MelansonTech/Melanson-Tech-Isolated-Shunt-Amplifier/Revision 1/TestData/BodePlots/1khz-10Meghz Gain 10x  0r010Shunt.xlsx

Untitled | Untitled 1 | Untitled 2 | Untitled 3
1000 | -0.166787 | -0.385627 | 0.336464
1258.925412 | -0.242249 | -0.413234 | 0.500956
1584.893192 | -0.150085 | -0.622799 | 0.415946
1995.262315 | -0.188624 | -0.812734 | 0.337932
2511.886432 | -0.183692 | -0.066411 | 0.445627
3162.27766 | -0.216886 | -0.911619 | 0.363395
3981.071706 | -0.248103 | -1.11181 | 0.502347
5011.872336 | -0.313746 | -1.38651 | 0.618555
6309.573445 | -0.263741 | -1.232366 | 0.56154
7943.282347 | -0.242898 | -1.544541 | 0.517559
10000 | -0.223894 | -1.853628 | 0.456404
12589.25412 | -0.209771 | -1.966123 | 0.607302
15848.93193 | -0.226493 | -3.019898 | 0.567094
19952.62315 | -0.173401 | -3.595255 | 0.597347
25118.86431 | -0.079341 | -4.264827 | 0.578082
31622.7766 | -0.080549 | -6.481584 | 0.593097
39810.71706 | 0.010377 | -8.275535 | 0.615941
50118.72336 | 0.131881 | -10.449231 | 0.556628
63095.73445 | 0.219651 | -13.857448 | 0.810801
79432.82347 | 0.352913 | -18.403695 | 0.686286
100000 | 0.480244 | -23.968928 | 0.706028
125892.5412 | 0.599213 | -30.235161 | 1.015421
158489.3192 | 0.776089 | -40.437328 | 0.848043
199526.2315 | 0.894499 | -51.551826 | 0.954622
251188.6432 | 1.355552 | -67.514444 | 1.121187
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
