MelansonTech/Melanson-Tech-Isolated-Shunt-Amplifier/Revision 1/TestData/BodePlots/1khz-10Meghz Gain 10x  0r010Shunt_1.xlsx

Untitled | Untitled 1 | Untitled 2 | Untitled 3
1000 | -0.164963 | -0.309048 | 0.379071
1079.775162 | -0.128116 | -0.219387 | 0.326995
1165.914401 | -0.161152 | -1.027728 | 0.403795
1258.925412 | -0.179917 | 0.23005 | 0.382496
1359.356391 | -0.142654 | -0.262303 | 0.411716
1467.799268 | -0.14915 | -0.528165 | 0.508479
1584.893192 | -0.144146 | -0.680492 | 0.357872
1711.328304 | -0.17431 | -0.493263 | 0.492636
1847.849797 | -0.179099 | -0.608428 | 0.557685
1995.262315 | -0.182238 | -0.674658 | 0.437536
2154.43469 | -0.187685 | -0.645897 | 0.421993
2326.305067 | -0.190564 | -0.792882 | 0.41525
2511.886432 | -0.228326 | -0.459325 | 0.386465
2712.272579 | -0.238131 | -0.811535 | 0.41732
2928.644565 | -0.208502 | -0.919118 | 0.406281
3162.27766 | -0.202652 | -0.95411 | 0.446176
3414.548874 | -0.216239 | -1.168893 | 0.458934
3686.945065 | -0.225559 | -0.89491 | 0.438337
3981.071706 | -0.226103 | -1.056473 | 0.480328
4298.662347 | -0.228212 | -1.099326 | 0.539283
4641.588834 | -0.244441 | -1.147914 | 0.468855
5011.872336 | -0.354077 | -0.637942 | 0.491152
5411.695265 | -0.244513 | -1.14488 | 0.51443
5843.414134 | -0.252042 | -1.434539 | 0.56404
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
