MelansonTech/Melanson-Tech-Isolated-Shunt-Amplifier/Revision 1/TestData/BodePlots/SI8921B-modifed/100khz-1000khz Gain 10x  0r010Shunt_3.3nf output filt C23-560pF - x50 filt cap 560pF.xlsx

Untitled | Untitled 1 | Untitled 2 | Untitled 3
1000 | -0.007271 | -0.572757 | 0.418006
1258.925412 | 0.077268 | -0.539768 | 0.400527
1584.893192 | -0.0003 | -0.723423 | 0.354738
1995.262315 | -0.01521 | -0.96655 | 0.359529
2511.886432 | -0.036307 | -1.231762 | 0.465736
3162.27766 | -0.059285 | -1.440721 | 0.452594
3981.071706 | -0.050049 | -1.825088 | 0.463353
5011.872336 | 0.00812 | -2.12929 | 0.626424
6309.573445 | -0.058686 | -2.53885 | 0.44223
7943.282347 | -0.059571 | -3.166069 | 0.462066
10000 | -0.060859 | -4.022216 | 0.529905
12589.25412 | -0.078112 | -5.213084 | 0.409742
15848.93193 | -0.039617 | -6.37527 | 0.570275
19952.62315 | 0.025826 | -8.159199 | 0.578589
25118.86431 | 0.125273 | -10.326592 | 0.628492
31622.7766 | 0.079798 | -13.222132 | 0.669211
39810.71706 | 0.114622 | -16.875604 | 0.748752
50118.72336 | 0.233843 | -21.505801 | 1.002004
63095.73445 | 0.16181 | -27.848137 | 0.795671
79432.82347 | 0.245553 | -35.295127 | 0.728898
100000 | 0.281433 | -45.062021 | 0.704041
125892.5412 | 0.12971 | -55.566231 | 0.908138
158489.3192 | 0.199942 | -73.108045 | 0.584394
199526.2315 | 0.116589 | -92.47451 | 0.797795
251188.6432 | -0.413037 | -119.043982 | 1.130682
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
