MelansonTech/Melanson-Tech-Isolated-Shunt-Amplifier/Revision 1/TestData/BodePlots/SI8921B-modifed/100khz-1000khz Gain 10x  0r010Shunt_3.3nf output filt C23-560pF.xlsx

Untitled | Untitled 1 | Untitled 2 | Untitled 3
100000 | 0.313502 | -41.958272 | 0.688879
125892.5412 | 0.387259 | -53.4945 | 0.875311
158489.3192 | 0.308083 | -67.947277 | 0.981933
199526.2315 | 0.115216 | -86.545426 | 0.829072
251188.6432 | -0.330637 | -107.270166 | 1.272936
316227.766 | -0.340213 | -139.088437 | 1.313568
398107.1706 | -0.810289 | -178.106699 | 1.503704
501187.2336 | -2.888756 | 126.559879 | 1.510791
630957.3445 | -5.692802 | 67.801909 | 1.687902
794328.2347 | -11.639043 | 0.706496 | 2.282123
1000000 | -17.937818 | -89.865859 | 8.847568
