MelansonTech/Melanson-Tech-Isolated-Shunt-Amplifier/Revision 1/TestData/BodePlots/SI8921B-modifed/100khz-1000khz Gain 50x  0r010Shunt_3.3nf output filt C23-560pF.xlsx

Untitled | Untitled 1 | Untitled 2 | Untitled 3
1000 | 0.064522 | -0.713499 | 0.825991
1258.925412 | 0.195579 | -1.837927 | 0.762102
1584.893192 | 0.099175 | -1.392925 | 0.747944
1995.262315 | 0.066472 | -1.645283 | 0.754356
2511.886432 | 0.068113 | -2.95294 | 0.716811
3162.27766 | 0.024284 | -2.597538 | 0.894711
3981.071706 | 0.010385 | -2.998652 | 0.720921
5011.872336 | 0.078165 | -4.980822 | 0.804446
6309.573445 | -0.016736 | -4.539137 | 0.83104
7943.282347 | -0.005151 | -5.303585 | 0.721352
10000 | -0.023023 | -6.788479 | 0.839424
12589.25412 | 0.063563 | -9.723817 | 0.912994
15848.93193 | -0.011544 | -10.399116 | 0.815987
19952.62315 | -0.036871 | -13.273732 | 0.986796
25118.86431 | 0.063136 | -17.025937 | 0.61663
31622.7766 | -0.061974 | -21.224436 | 0.837353
39810.71706 | -0.025154 | -26.655559 | 1.012666
50118.72336 | 0.028295 | -32.734162 | 0.830485
63095.73445 | -0.151455 | -42.932902 | 1.357885
79432.82347 | -0.375164 | -54.226394 | 1.439817
100000 | -0.672215 | -67.874812 | 1.704844
125892.5412 | -1.923903 | -82.940608 | 1.889883
158489.3192 | -1.967661 | -106.971336 | 2.29011
199526.2315 | -3.207152 | -131.090175 | 2.251656
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
