MelansonTech/Melanson-Tech-Isolated-Shunt-Amplifier/Revision 1/TestData/BodePlots/SI8921B-modifed/100khz-100khz Gain 50x  0r010Shunt_3.3nf output filt C23-560pF - x50 filt cap 560pF.xlsx

Untitled | Untitled 1 | Untitled 2 | Untitled 3
1000 | 0.05207 | -1.963352 | 0.942213
1258.925412 | 0.197826 | -4.049852 | 0.917636
1584.893192 | 0.071184 | -3.003377 | 0.739586
1995.262315 | 0.039404 | -3.660843 | 0.793368
2511.886432 | 0.101302 | -5.543226 | 0.779344
3162.27766 | -0.014446 | -5.522928 | 0.740511
3981.071706 | -0.029404 | -7.030474 | 0.796969
5011.872336 | 0.05596 | -9.691169 | 0.747881
6309.573445 | -0.105583 | -10.825865 | 0.732612
7943.282347 | -0.118312 | -13.497003 | 0.750385
10000 | -0.181516 | -17.000783 | 0.781518
12589.25412 | -0.160564 | -20.839707 | 0.88175
15848.93193 | -0.395699 | -26.29038 | 0.732019
19952.62315 | -0.556081 | -32.826666 | 0.730841
25118.86431 | -0.858598 | -42.349229 | 1.010743
31622.7766 | -1.349577 | -50.452464 | 0.886223
39810.71706 | -1.926483 | -61.54613 | 0.655165
50118.72336 | -2.974799 | -76.441642 | 0.9142
63095.73445 | -3.834709 | -90.704306 | 0.788833
79432.82347 | -5.340546 | -108.032392 | 0.944281
100000 | -7.123333 | -126.834246 | 0.977973
