MelansonTech/Melanson-Tech-Isolated-Shunt-Amplifier/Revision 1/TestData/BodePlots/SI8921B-modifed/1khz-1000khz Gain 10x  0r010Shunt_3.3nf output filt C23-560pF - x50 filt cap 560pF filt cap2 47nF.xlsx

Untitled | Untitled 1 | Untitled 2 | Untitled 3
1000 | -0.001412 | -0.491789 | 0.386197
1258.925412 | 0.051911 | -0.882857 | 0.382758
1584.893192 | -0.002914 | -0.627658 | 0.3803
1995.262315 | -0.004918 | -0.985267 | 0.391553
2511.886432 | 0.058918 | -0.762546 | 0.44308
3162.27766 | -0.03218 | -1.502325 | 0.417804
3981.071706 | -0.047722 | -1.692322 | 0.447256
5011.872336 | -0.068907 | -2.207698 | 0.52855
6309.573445 | -0.031446 | -2.486523 | 0.346339
7943.282347 | -0.03868 | -3.176357 | 0.403295
10000 | -0.035435 | -4.062742 | 0.529503
12589.25412 | 0.118613 | -5.158486 | 0.474753
15848.93193 | 0.008463 | -6.300188 | 0.509958
19952.62315 | 0.037662 | -8.071385 | 0.50475
25118.86431 | 0.045896 | -11.128869 | 0.686767
31622.7766 | 0.071791 | -13.162034 | 0.622529
39810.71706 | 0.154046 | -16.970277 | 0.615668
50118.72336 | 0.138483 | -21.865062 | 0.714991
63095.73445 | 0.204389 | -28.370627 | 0.828323
79432.82347 | 0.26264 | -35.456147 | 0.795539
100000 | 0.289751 | -45.445786 | 0.623059
125892.5412 | -0.226415 | -55.959106 | 0.780761
158489.3192 | 0.161721 | -73.118075 | 0.864599
199526.2315 | 0.007809 | -92.832452 | 1.103654
251188.6432 | -0.325714 | -118.690986 | 1.269356
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
