MelansonTech/Melanson-Tech-Isolated-Shunt-Amplifier/Revision 1/TestData/BodePlots/SI8921B-modifed/1khz-1000khz Gain 10x  0r010Shunt_3.3nf output filt C23-560pF.xlsx

Untitled | Untitled 1 | Untitled 2 | Untitled 3
1000 | -0.029164 | -0.415758 | 0.409154
1258.925412 | 0.051928 | -0.653245 | 0.450997
1584.893192 | 0.008203 | -0.673949 | 0.384839
1995.262315 | -0.003543 | -0.855599 | 0.388993
2511.886432 | -0.028419 | -1.35738 | 0.394654
3162.27766 | -0.029335 | -1.346178 | 0.401389
3981.071706 | -0.046099 | -1.487113 | 0.375325
5011.872336 | -0.088454 | -1.963935 | 0.467691
6309.573445 | -0.040359 | -2.587683 | 0.367528
7943.282347 | -0.039981 | -2.78341 | 0.512421
10000 | -0.030514 | -3.598115 | 0.436275
12589.25412 | 0.052237 | -4.786346 | 0.506834
15848.93193 | 0.015761 | -5.972702 | 0.533102
19952.62315 | 0.048069 | -7.253569 | 0.629485
25118.86431 | 0.112095 | -8.332555 | 0.620274
31622.7766 | 0.151572 | -12.033556 | 0.669804
39810.71706 | 0.187474 | -15.449311 | 0.57619
50118.72336 | 0.348314 | -20.808378 | 0.752883
63095.73445 | 0.304537 | -25.765356 | 0.763022
79432.82347 | 0.328061 | -32.978392 | 0.748215
100000 | 0.354872 | -42.197753 | 0.654933
125892.5412 | 0.250991 | -51.815006 | 0.888359
158489.3192 | 0.305403 | -67.868428 | 0.809862
199526.2315 | 0.134738 | -86.163011 | 0.788386
251188.6432 | -0.074423 | -110.093568 | 1.306668
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
