MelansonTech/Melanson-Tech-Isolated-Shunt-Amplifier/Revision 1/TestData/BodePlots/SI8921B-modifed/1khz-100khz Gain 50x  0r010Shunt_3.3nf output filt C23-560pF - x50 filt cap 560pF filt cap2 47nF.xlsx

Untitled | Untitled 1 | Untitled 2 | Untitled 3
1000 | 0.071029 | -3.649681 | 0.701021
1258.925412 | 0.25024 | -5.870788 | 0.806356
1584.893192 | 0.064123 | -5.633435 | 0.673676
1995.262315 | 0.04073 | -7.223179 | 0.845832
2511.886432 | 0.15908 | -9.99452 | 0.822513
3162.27766 | -0.052469 | -11.215229 | 0.658098
3981.071706 | -0.085104 | -14.04281 | 0.714957
5011.872336 | -0.041204 | -18.347498 | 0.854144
6309.573445 | -0.255909 | -21.661879 | 0.841967
7943.282347 | -0.369085 | -27.022767 | 0.90138
10000 | -0.556596 | -33.566681 | 0.999071
12589.25412 | -0.6651 | -41.955037 | 1.026333
15848.93193 | -1.34603 | -51.607566 | 0.877883
19952.62315 | -1.996641 | -63.266367 | 0.854583
25118.86431 | -3.127706 | -76.344589 | 0.893428
31622.7766 | -4.274065 | -92.964914 | 0.907988
39810.71706 | -5.980007 | -110.229574 | 1.189904
50118.72336 | -8.540003 | -129.364359 | 1.175728
63095.73445 | -10.794905 | -150.328231 | 1.426667
79432.82347 | -14.107479 | -171.989133 | 2.210238
100000 | -17.905938 | 165.209907 | 5.050973
