MelansonTech/Melanson-Tech-Isolated-Shunt-Amplifier/Revision 1/TestData/BodePlots/SI8921B-modifed/1khz-800khz Gain 10x  0r010Shunt_3.3nf output filt.xlsx

Untitled | Untitled 1 | Untitled 2 | Untitled 3
1000 | 0.007174 | -0.387205 | 0.400885
1258.925412 | 0.045516 | -0.304139 | 0.429812
1584.893192 | 0.013161 | -0.63136 | 0.355633
1995.262315 | 0.002602 | -0.874513 | 0.411591
2511.886432 | -0.018299 | -1.251431 | 0.381355
3162.27766 | -0.034086 | -1.198722 | 0.366614
3981.071706 | -0.052975 | -1.567748 | 0.383089
5011.872336 | -0.101388 | -2.345715 | 0.369202
6309.573445 | -0.049839 | -2.11402 | 0.478531
7943.282347 | -0.041625 | -2.653531 | 0.416471
10000 | -0.036766 | -3.265254 | 0.398806
12589.25412 | -0.035812 | -4.308069 | 0.607169
15848.93193 | 0.04319 | -5.508472 | 0.54892
19952.62315 | 0.056539 | -6.856632 | 0.482075
25118.86431 | 0.282153 | -8.498182 | 0.818443
31622.7766 | 0.142533 | -11.072022 | 0.608683
39810.71706 | 0.214596 | -14.57403 | 0.459452
50118.72336 | 0.231782 | -19.186235 | 1.108948
63095.73445 | 0.294758 | -23.97433 | 0.719064
79432.82347 | 0.419715 | -30.905854 | 0.901599
100000 | 0.54491 | -39.832185 | 0.638091
125892.5412 | 0.48953 | -49.518875 | 0.84785
158489.3192 | 0.550398 | -65.048945 | 0.820462
199526.2315 | 0.608525 | -83.836701 | 0.648542
251188.6432 | 0.476222 | -108.164402 | 0.913757
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
