MelansonTech/Melanson-Tech-Isolated-Shunt-Amplifier/Revision 1/TestData/BodePlots/SI8921B-modifed/1khz-800khz Gain 10x  0r010Shunt_3.3nf output filt_1.xlsx

Untitled | Untitled 1 | Untitled 2 | Untitled 3
1000 | -0.011512 | -0.400714 | 0.342174
1258.925412 | 0.025063 | -0.880549 | 0.415367
1584.893192 | 0.018192 | -0.721981 | 0.420674
1995.262315 | 0.003419 | -0.833224 | 0.403585
2511.886432 | 0.015298 | -1.158992 | 0.400182
3162.27766 | -0.052222 | -1.268797 | 0.398517
3981.071706 | -0.049142 | -1.533551 | 0.413095
5011.872336 | -0.01116 | -2.216545 | 0.377675
6309.573445 | -0.052252 | -2.190339 | 0.533511
7943.282347 | -0.035679 | -2.711656 | 0.596563
10000 | -0.038416 | -3.271058 | 0.461868
12589.25412 | 0.094113 | -4.486929 | 0.544178
15848.93193 | 0.041698 | -5.391758 | 0.565729
19952.62315 | 0.06628 | -6.991664 | 0.59351
25118.86431 | 0.2137 | -8.668189 | 0.624129
31622.7766 | 0.132644 | -11.482407 | 0.66954
39810.71706 | 0.20789 | -14.715592 | 0.832414
50118.72336 | 0.360193 | -19.034826 | 0.659566
63095.73445 | 0.367586 | -24.342496 | 0.746998
79432.82347 | 0.401086 | -31.224258 | 0.883342
100000 | 0.471592 | -40.172128 | 0.821223
125892.5412 | 0.364402 | -49.968074 | 1.061229
158489.3192 | 0.610198 | -66.053959 | 0.822275
199526.2315 | 0.640646 | -83.803273 | 0.649341
251188.6432 | 0.171551 | -108.385574 | 1.39107
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
