MelansonTech/Melanson-Tech-Isolated-Shunt-Amplifier/Revision 1/TestData/BodePlots/SI8921B-modifed/1khz-800khz Gain 50x  0r010Shunt_3.3nf output filt C23-680pF.xlsx

Untitled | Untitled 1 | Untitled 2 | Untitled 3
100000 | 0.125335 | -44.095085 | 0.659089
125892.5412 | -0.27493 | -55.399287 | 0.824094
158489.3192 | -0.171427 | -70.275468 | 1.0017
199526.2315 | -0.391973 | -88.667018 | 0.886321
251188.6432 | -0.718177 | -113.174029 | 0.872392
316227.766 | -0.987231 | -139.91413 | 1.307415
398107.1706 | -1.628402 | -178.534868 | 1.041197
501187.2336 | -3.15011 | 125.299528 | 1.797763
630957.3445 | -6.27653 | 67.748488 | 1.955576
794328.2347 | -12.194439 | 1.348629 | 2.595551
1000000 | -19.093066 | -77.022631 | 7.16214
