MelansonTech/Melanson-Tech-Isolated-Shunt-Amplifier/Revision 1/TestData/BodePlots/SI8921B-modifed/1khz-800khz Gain 50x  0r010Shunt_3.3nf output filt.xlsx

Untitled | Untitled 1 | Untitled 2 | Untitled 3
1000 | 0.054281 | -0.672905 | 0.793062
1258.925412 | 0.170075 | -1.723295 | 0.784336
1584.893192 | 0.081743 | -1.191481 | 0.767433
1995.262315 | 0.062793 | -1.538392 | 0.818119
2511.886432 | 0.147071 | -2.645347 | 0.845907
3162.27766 | -0.003843 | -2.208584 | 0.847037
3981.071706 | 0.008742 | -2.786028 | 0.736751
5011.872336 | 0.039246 | -4.215678 | 0.802545
6309.573445 | -0.027557 | -4.0071 | 0.901875
7943.282347 | -0.027034 | -4.934049 | 0.770238
10000 | -0.03041 | -6.192249 | 0.822031
12589.25412 | 0.046377 | -8.37912 | 0.744522
15848.93193 | 0.001363 | -10.06228 | 0.93926
19952.62315 | -0.024831 | -12.176484 | 1.018673
25118.86431 | 0.036893 | -16.185266 | 0.853329
31622.7766 | 0.024304 | -19.567205 | 0.875395
39810.71706 | 0.075147 | -24.680836 | 1.123904
50118.72336 | -0.131459 | -31.30462 | 1.181298
63095.73445 | -0.029736 | -40.1159 | 1.648383
79432.82347 | -0.102527 | -50.902239 | 1.566692
100000 | -0.279003 | -64.228459 | 1.872802
125892.5412 | -1.556058 | -79.621167 | 2.400331
158489.3192 | -1.220001 | -102.288345 | 2.809618
199526.2315 | -2.305808 | -127.616955 | 2.577078
251188.6432 | -3.266524 | -155.787252 | 2.731802
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
