MelansonTech/Melanson-Tech-Isolated-Shunt-Amplifier/Revision 1/TestData/BodePlots/SI8921B/100hz-1Mkhz Gain 100x  0r010Shunt_2.2nf output filt.xlsx

Untitled | Untitled 1 | Untitled 2 | Untitled 3
100 | 0.006271 | -0.068033 | 0.27774
125.892541 | -0.026333 | 0.222918 | 0.290215
158.489319 | 0.003324 | 0.042885 | 0.329393
199.526231 | -0.006859 | 0.049974 | 0.350675
251.188643 | -0.00971 | -0.275637 | 0.354524
316.227766 | 7.2e-05 | 0.090136 | 0.290524
398.107171 | -0.006296 | 0.0268 | 0.326617
501.187234 | 0.069499 | 0.150467 | 0.299249
630.957344 | 0.014773 | 0.012803 | 0.286016
794.328235 | 0.037272 | 0.165785 | 0.346965
1000 | 0.024027 | 0.075002 | 0.388099
1258.925412 | 0.105147 | -0.28254 | 0.356661
1584.893192 | 0.065292 | -0.021393 | 0.40356
1995.262315 | 0.05624 | -0.055238 | 0.401904
2511.886432 | 0.049367 | 0.192684 | 0.400087
3162.27766 | 0.071064 | -0.111055 | 0.427408
3981.071706 | 0.0964 | -0.065856 | 0.372432
5011.872336 | 0.149708 | -0.680933 | 0.414754
6309.573445 | 0.190248 | -0.612579 | 0.374768
7943.282347 | 0.256524 | -0.993632 | 0.388619
10000 | 0.326169 | -1.776701 | 0.412916
12589.25412 | 0.357161 | -2.962147 | 0.540464
15848.93193 | 0.420766 | -4.036209 | 0.661014
19952.62315 | 0.464666 | -5.588194 | 0.489353
25118.86431 | 0.612346 | -8.454723 | 0.608499
31622.7766 | 0.560109 | -10.081403 | 0.549657
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
