MelansonTech/Melanson-Tech-Isolated-Shunt-Amplifier/Revision 1/TestData/BodePlots/SI8921B/100hz-1Mkhz Gain 100x  0r010Shunt_3.3nf output filt.xlsx

Untitled | Untitled 1 | Untitled 2 | Untitled 3
100 | -0.022282 | -0.058049 | 0.313225
125.892541 | -0.044786 | -0.046411 | 0.296977
158.489319 | -0.024129 | 0.030752 | 0.380635
199.526231 | -0.005085 | 0.061221 | 0.346586
251.188643 | -0.053261 | -0.192632 | 0.401592
316.227766 | -0.005653 | 0.169307 | 0.325114
398.107171 | -0.016431 | 0.099411 | 0.332158
501.187234 | 0.010859 | -0.084321 | 0.328726
630.957344 | 0.009812 | -0.043785 | 0.368432
794.328235 | 0.030827 | 0.10783 | 0.391994
1000 | 0.021412 | 0.023076 | 0.334639
1258.925412 | 0.028485 | -0.340813 | 0.349454
1584.893192 | 0.061199 | 0.012489 | 0.371446
1995.262315 | 0.050718 | -0.149597 | 0.384132
2511.886432 | 0.052177 | -0.195681 | 0.47576
3162.27766 | 0.057638 | -0.224039 | 0.436108
3981.071706 | 0.088252 | -0.256186 | 0.328084
5011.872336 | 0.102445 | -0.62421 | 0.375166
6309.573445 | 0.20179 | -0.731505 | 0.366793
7943.282347 | 0.247345 | -1.369095 | 0.381789
10000 | 0.320085 | -2.050848 | 0.402476
12589.25412 | 0.322192 | -3.010692 | 0.365105
15848.93193 | 0.427328 | -4.69689 | 0.474706
19952.62315 | 0.466185 | -6.319212 | 0.464672
25118.86431 | 0.497584 | -7.890442 | 0.594781
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
