MelansonTech/Melanson-Tech-Isolated-Shunt-Amplifier/Revision 1/TestData/BodePlots/SI8921B/100hz-1Mkhz Gain 100x  0r010Shunt_4nf output filt.xlsx

Untitled | Untitled 1 | Untitled 2 | Untitled 3
100 | -0.011646 | -0.186644 | 0.324419
125.892541 | -0.008848 | -0.470833 | 0.374328
158.489319 | 0.000513 | -0.054358 | 0.332091
199.526231 | -0.014627 | 0.00252 | 0.31939
251.188643 | -0.035922 | -0.133026 | 0.338004
316.227766 | -0.003355 | 0.055016 | 0.286123
398.107171 | -0.020003 | 0.102376 | 0.351795
501.187234 | 0.130507 | -0.197465 | 0.432652
630.957344 | 0.016004 | 0.028714 | 0.370028
794.328235 | 0.027295 | 0.040367 | 0.362361
1000 | 0.021116 | 0.040315 | 0.331496
1258.925412 | 0.028183 | 0.166917 | 0.348732
1584.893192 | 0.035851 | -0.121835 | 0.417872
1995.262315 | 0.05675 | -0.181759 | 0.420646
2511.886432 | 0.10589 | -0.397403 | 0.394932
3162.27766 | 0.073821 | -0.241463 | 0.400716
3981.071706 | 0.104705 | -0.412814 | 0.427394
5011.872336 | 0.202215 | -0.87855 | 0.446382
6309.573445 | 0.215852 | -0.99377 | 0.364387
7943.282347 | 0.247451 | -1.597763 | 0.380991
10000 | 0.319096 | -2.297543 | 0.426298
12589.25412 | 0.426062 | -3.911501 | 0.507399
15848.93193 | 0.418839 | -5.079229 | 0.549556
19952.62315 | 0.465758 | -7.025158 | 0.553534
25118.86431 | 0.623222 | -8.69878 | 0.623135
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
