MelansonTech/Melanson-Tech-Isolated-Shunt-Amplifier/Revision 1/TestData/BodePlots/SI8921B/100hz-200khz Gain 100x  0r010Shunt_4.7nf output filt.xlsx

Untitled | Untitled 1 | Untitled 2 | Untitled 3
100 | -0.018273 | 0.063398 | 0.346112
125.892541 | 0.047429 | -0.108282 | 0.349609
158.489319 | -0.017419 | 0.007446 | 0.314467
199.526231 | -0.008665 | -0.04091 | 0.364519
251.188643 | -0.003899 | -0.112408 | 0.355988
316.227766 | -0.008815 | -0.03527 | 0.287034
398.107171 | -0.014407 | 0.063112 | 0.321475
501.187234 | 0.059367 | -0.076349 | 0.43115
630.957344 | 0.011782 | -0.062217 | 0.329315
794.328235 | 0.018064 | 0.046277 | 0.398337
1000 | 0.024427 | 0.038161 | 0.345292
1258.925412 | 0.164085 | -0.389204 | 0.359969
1584.893192 | 0.063465 | -0.091607 | 0.383588
1995.262315 | 0.059882 | -0.103315 | 0.363583
2511.886432 | 0.066218 | -0.417576 | 0.414248
3162.27766 | 0.074538 | -0.325521 | 0.420616
3981.071706 | 0.10865 | -0.417827 | 0.368795
5011.872336 | 0.217314 | -0.364807 | 0.437818
6309.573445 | 0.185893 | -0.960475 | 0.400954
7943.282347 | 0.259456 | -1.634621 | 0.429875
10000 | 0.331057 | -2.478709 | 0.500724
12589.25412 | 0.410079 | -3.952926 | 0.477189
15848.93193 | 0.418411 | -5.221231 | 0.377721
19952.62315 | 0.457637 | -6.920653 | 0.545664
25118.86431 | 0.614109 | -9.375478 | 0.574576
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
