MelansonTech/Melanson-Tech-Isolated-Shunt-Amplifier/Revision 1/TestData/BodePlots/SI8921B/100hz-200khz Gain 100x  0r010Shunt_6.8nf output filt.xlsx

Untitled | Untitled 1 | Untitled 2 | Untitled 3
100 | -0.044396 | -0.130725 | 0.326539
125.892541 | -0.093795 | 0.491135 | 0.321192
158.489319 | -0.017354 | 0.145234 | 0.291424
199.526231 | -0.016703 | -0.091684 | 0.37555
251.188643 | 0.039367 | -0.027676 | 0.337361
316.227766 | -0.028107 | -0.106062 | 0.333925
398.107171 | -0.01526 | -0.235397 | 0.367369
501.187234 | 0.068549 | 0.212462 | 0.357161
630.957344 | -0.00204 | -0.475658 | 0.323669
794.328235 | 0.021351 | -0.566453 | 0.329117
1000 | 0.018558 | -0.612416 | 0.401373
1258.925412 | 0.104122 | -0.784801 | 0.350368
1584.893192 | 0.016642 | -1.42983 | 0.414748
1995.262315 | 0.049805 | -1.416681 | 0.369812
2511.886432 | 0.052775 | -2.520295 | 0.433273
3162.27766 | 0.063683 | -2.143986 | 0.314412
3981.071706 | 0.070977 | -3.084316 | 0.313028
5011.872336 | 0.12525 | -4.638268 | 0.349495
6309.573445 | 0.173352 | -4.940526 | 0.337103
7943.282347 | 0.217617 | -6.778015 | 0.391525
10000 | 0.249068 | -9.034566 | 0.367027
12589.25412 | 0.341007 | -11.79022 | 0.360414
15848.93193 | 0.334261 | -15.607988 | 0.311247
19952.62315 | 0.335615 | -20.002143 | 0.360435
25118.86431 | 0.393172 | -24.640276 | 0.29253
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
