MelansonTech/Melanson-Tech-Isolated-Shunt-Amplifier/Revision 1/TestData/BodePlots/SI8921B/1khz-1Meghz Gain 100x  0r010Shunt_1.xlsx

Untitled | Untitled 1 | Untitled 2 | Untitled 3
100 | -0.040266 | -0.300635 | 0.367372
125.892541 | -0.0684 | -0.857715 | 0.329266
158.489319 | -0.073799 | -0.877054 | 0.345439
199.526231 | -0.050687 | -0.956209 | 0.332939
251.188643 | 0.013784 | -1.630337 | 0.365851
316.227766 | -0.05302 | -1.543089 | 0.350905
398.107171 | -0.052236 | -1.930627 | 0.323077
501.187234 | -0.002989 | -3.066693 | 0.368959
630.957344 | -0.041466 | -3.257414 | 0.323452
794.328235 | -0.058252 | -3.992169 | 0.356434
1000 | -0.047547 | -5.068577 | 0.417599
1258.925412 | -0.074442 | -6.766694 | 0.316775
1584.893192 | -0.118696 | -8.132802 | 0.409646
1995.262315 | -0.180433 | -10.141456 | 0.353288
2511.886432 | -0.238975 | -12.34969 | 0.415411
3162.27766 | -0.432187 | -15.518061 | 0.326305
3981.071706 | -0.635824 | -19.2479 | 0.295284
5011.872336 | -0.905451 | -23.176625 | 0.3543
6309.573445 | -1.35525 | -28.242763 | 0.314673
7943.282347 | -1.911247 | -33.786021 | 0.326258
10000 | -2.669884 | -39.622342 | 0.426241
12589.25412 | -3.572684 | -43.689785 | 0.650378
15848.93193 | -4.800547 | -51.038006 | 1.011903
19952.62315 | -6.139868 | -55.657167 | 0.997515
