MelansonTech/Melanson-Tech-Isolated-Shunt-Amplifier/Revision 1/TestData/BodePlots/SI8921B/1khz-1Meghz Gain 100x  0r010Shunt_10nf output filt.xlsx

Untitled | Untitled 1 | Untitled 2 | Untitled 3
10000 | 0.300048 | -4.686134 | 0.371065
12589.25412 | 0.350135 | -6.141829 | 0.409016
15848.93193 | 0.370621 | -8.473006 | 0.327902
19952.62315 | 0.381899 | -11.277017 | 0.467201
25118.86431 | 0.520764 | -15.149394 | 0.585185
31622.7766 | 0.361606 | -19.039818 | 0.487492
39810.71706 | 0.340702 | -24.200139 | 0.490641
50118.72336 | 0.321734 | -30.414533 | 0.649621
63095.73445 | 0.156017 | -39.263794 | 0.537156
79432.82347 | -0.088307 | -48.838645 | 0.502119
100000 | -0.425278 | -61.119064 | 0.560136
125892.5412 | -1.410881 | -73.225353 | 0.631223
158489.3192 | -1.762977 | -93.561768 | 0.900835
199526.2315 | -2.70213 | -113.870851 | 0.91062
251188.6432 | -4.129018 | -137.634049 | 1.271432
316227.766 | -5.228257 | -167.954733 | 1.462116
398107.1706 | -6.70648 | 154.027069 | 1.748049
501187.2336 | -8.890412 | 102.430688 | 2.305689
630957.3445 | -13.274978 | 49.262428 | 3.598222
794328.2347 | -18.892244 | -13.599232 | 7.016472
1000000 | -31.557729 | 78.950848 | 50.901109
