MelansonTech/Melanson-Tech-Isolated-Shunt-Amplifier/Revision 1/TestData/BodePlots/SI8921B/1khz-1Meghz Gain 100x  0r010Shunt_2.2nf output filt.xlsx

Untitled | Untitled 1 | Untitled 2 | Untitled 3
10000 | 0.323687 | -1.745681 | 0.454382
12589.25412 | 0.382882 | -3.138565 | 0.514142
15848.93193 | 0.407829 | -4.127574 | 0.44463
19952.62315 | 0.455105 | -5.607695 | 0.479115
25118.86431 | 0.61392 | -8.099042 | 0.635949
31622.7766 | 0.545158 | -9.946099 | 0.639135
39810.71706 | 0.618791 | -13.261553 | 0.64644
50118.72336 | 0.663226 | -16.347834 | 1.150049
63095.73445 | 0.72475 | -22.087686 | 0.942416
79432.82347 | 0.84102 | -28.678151 | 0.728902
100000 | 0.922953 | -36.839642 | 0.85791
125892.5412 | 0.889272 | -45.889181 | 0.848671
158489.3192 | 1.022664 | -60.165138 | 0.759502
199526.2315 | 1.037941 | -77.371936 | 0.842674
251188.6432 | 0.075321 | -97.605583 | 1.411098
316227.766 | 1.14749 | -127.365566 | 0.848284
398107.1706 | 0.651625 | -163.264816 | 0.902364
501187.2336 | 0.032035 | 146.427866 | 2.00602
630957.3445 | -3.043097 | 86.635377 | 1.650604
794328.2347 | -8.158242 | 18.046868 | 1.895639
1000000 | -15.109239 | -54.301349 | 5.183794
