MelansonTech/Melanson-Tech-Isolated-Shunt-Amplifier/Revision 1/TestData/BodePlots/SI8921B/1khz-1Meghz Gain 100x  0r010Shunt_2nf output filt.xlsx

Untitled | Untitled 1 | Untitled 2 | Untitled 3
10000 | 0.294859 | -1.509498 | 0.423811
12589.25412 | 0.433143 | -3.051832 | 0.476017
15848.93193 | 0.425297 | -4.1213 | 0.580953
19952.62315 | 0.473681 | -5.423894 | 0.458336
25118.86431 | 0.564691 | -7.214792 | 0.460106
31622.7766 | 0.553752 | -9.938899 | 0.510657
39810.71706 | 0.635776 | -12.780403 | 0.615967
50118.72336 | 0.699175 | -17.344241 | 0.814612
63095.73445 | 0.76438 | -21.94672 | 0.861588
79432.82347 | 0.853398 | -28.130204 | 0.839258
100000 | 0.93582 | -36.536057 | 0.840661
125892.5412 | 0.958983 | -45.673748 | 1.418019
158489.3192 | 1.060342 | -59.541483 | 0.871163
199526.2315 | 1.084826 | -76.019126 | 0.838881
251188.6432 | 0.830972 | -97.195667 | 0.77354
316227.766 | 1.132826 | -124.009865 | 0.849915
398107.1706 | 0.926832 | -160.808537 | 1.040071
501187.2336 | 0.687452 | 146.499576 | 2.000071
630957.3445 | -2.888779 | 92.346553 | 1.151706
794328.2347 | -7.500326 | 23.819562 | 1.566643
1000000 | -13.940191 | -45.762394 | 4.927294
