MelansonTech/Melanson-Tech-Isolated-Shunt-Amplifier/Revision 1/TestData/BodePlots/SI8921B/1khz-1Meghz Gain 10x  0r010Shunt.xlsx

Untitled | Untitled 1 | Untitled 2 | Untitled 3
100 | -0.011974 | 0.027348 | 0.353616
125.892541 | -0.036462 | 0.125168 | 0.26227
158.489319 | -0.005195 | 0.078193 | 0.296938
199.526231 | 0.012028 | 0.01086 | 0.305197
251.188643 | -0.041303 | -0.301508 | 0.362601
316.227766 | -0.004155 | 0.112693 | 0.345618
398.107171 | 0.001361 | 0.142392 | 0.368232
501.187234 | 0.030764 | -0.236163 | 0.396907
630.957344 | 0.013538 | 0.159618 | 0.380151
794.328235 | 0.026754 | 0.13517 | 0.40294
1000 | 0.040398 | 0.237857 | 0.358591
1258.925412 | 0.078803 | -0.071533 | 0.39362
1584.893192 | 0.052961 | 0.119723 | 0.342414
1995.262315 | 0.069853 | 0.07897 | 0.41962
2511.886432 | 0.081556 | -0.496201 | 0.435972
3162.27766 | 0.079251 | 0.049528 | 0.411636
3981.071706 | 0.09629 | 0.036167 | 0.33583
5011.872336 | 0.139264 | -0.55178 | 0.407729
6309.573445 | 0.180051 | -0.156377 | 0.420704
7943.282347 | 0.244452 | -0.716448 | 0.398787
10000 | 0.312592 | -1.563412 | 0.388825
12589.25412 | 0.342333 | -2.199113 | 0.436873
15848.93193 | 0.409261 | -3.263344 | 0.434955
19952.62315 | 0.47255 | -4.753161 | 0.433694
25118.86431 | 0.597106 | -6.564843 | 0.493856
31622.7766 | 0.538456 | -8.812895 | 0.60698
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
