MelansonTech/Melanson-Tech-Isolated-Shunt-Amplifier/Revision 1/TestData/BodePlots/SI8921B/1khz-660Khz Gain 100x  0r010Shunt_2.2nf output filt.xlsx

Untitled | Untitled 1 | Untitled 2 | Untitled 3
10000 | 0.314392 | -1.720821 | 0.42763
12589.25412 | 0.422342 | -2.639033 | 0.38942
15848.93193 | 0.424993 | -3.943693 | 0.420316
19952.62315 | 0.47389 | -5.691468 | 0.538683
25118.86431 | 0.583355 | -7.365163 | 0.622875
31622.7766 | 0.563041 | -10.142486 | 0.541522
39810.71706 | 0.628358 | -13.038319 | 0.693177
50118.72336 | 0.728325 | -16.311419 | 0.873984
63095.73445 | 0.784159 | -22.242613 | 0.913689
79432.82347 | 0.816455 | -28.693135 | 1.016865
100000 | 0.918208 | -36.790674 | 0.854817
125892.5412 | 0.691173 | -45.120989 | 0.810227
158489.3192 | 1.035842 | -60.69361 | 0.699224
199526.2315 | 1.02196 | -77.457352 | 0.938489
251188.6432 | 0.601451 | -99.52572 | 1.000351
316227.766 | 0.946779 | -126.62727 | 1.311761
398107.1706 | 0.698345 | -163.731703 | 1.316802
501187.2336 | 0.822028 | 152.377264 | 2.632393
630957.3445 | -3.310619 | 88.000965 | 1.357887
