MelansonTech/Melanson-Tech-Isolated-Shunt-Amplifier/Revision 1/TestData/BodePlots/SI8921B/1khz-800khz Gain 100x  0r010Shunt_4.7nf output filt (C18+C16 10pF).xlsx

Untitled | Untitled 1 | Untitled 2 | Untitled 3
1000 | 0.013726 | -0.098492 | 0.375031
1258.925412 | 0.146983 | -0.391426 | 0.396714
1584.893192 | 0.051566 | -0.283347 | 0.397007
1995.262315 | 0.060029 | -0.173025 | 0.399271
2511.886432 | 0.049773 | -0.101452 | 0.447835
3162.27766 | 0.061521 | -0.309518 | 0.397814
3981.071706 | 0.089867 | -0.44432 | 0.434802
5011.872336 | 0.163113 | -0.918733 | 0.45314
6309.573445 | 0.207162 | -1.203555 | 0.465547
7943.282347 | 0.235537 | -1.902127 | 0.344218
10000 | 0.289501 | -2.859301 | 0.472498
12589.25412 | 0.53855 | -3.743801 | 0.534384
15848.93193 | 0.409707 | -5.648812 | 0.564252
19952.62315 | 0.476892 | -7.545591 | 0.604356
25118.86431 | 0.54456 | -10.444291 | 0.627787
31622.7766 | 0.575603 | -12.883252 | 0.658921
39810.71706 | 0.599295 | -17.06026 | 0.573339
50118.72336 | 0.663205 | -21.346372 | 0.909075
63095.73445 | 0.660213 | -28.539854 | 0.60682
79432.82347 | 0.710457 | -36.347691 | 0.833554
100000 | 0.771053 | -46.607654 | 0.800096
125892.5412 | 0.618028 | -57.862247 | 0.788381
158489.3192 | 0.55105 | -75.372497 | 0.613099
199526.2315 | 0.277929 | -95.591859 | 0.604647
251188.6432 | -0.409585 | -124.092448 | 1.044228
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
