MelansonTech/Melanson-Tech-Isolated-Shunt-Amplifier/Revision 1/TestData/BodePlots/SI8921B/1khz-800khz Gain 100x  0r010Shunt_4.7nf output filt (C18+C16 20pF).xlsx

Untitled | Untitled 1 | Untitled 2 | Untitled 3
1000 | 0.025474 | 0.031933 | 0.375061
1258.925412 | 0.042194 | -0.559746 | 0.357387
1584.893192 | 0.054001 | -0.136177 | 0.373447
1995.262315 | 0.05323 | -0.306063 | 0.401677
2511.886432 | 0.069746 | -0.493142 | 0.396314
3162.27766 | 0.041455 | -0.451586 | 0.409853
3981.071706 | 0.091062 | -0.630836 | 0.440385
5011.872336 | 0.149384 | -1.169144 | 0.338544
6309.573445 | 0.194679 | -1.260288 | 0.406192
7943.282347 | 0.233294 | -2.095422 | 0.336717
10000 | 0.28815 | -3.211807 | 0.368621
12589.25412 | 0.364146 | -3.987879 | 0.420434
15848.93193 | 0.422129 | -6.125335 | 0.503746
19952.62315 | 0.436998 | -8.28406 | 0.463437
25118.86431 | 0.540288 | -10.533268 | 0.489041
31622.7766 | 0.528598 | -14.238631 | 0.66276
39810.71706 | 0.586724 | -18.355318 | 0.551106
50118.72336 | 0.57378 | -23.158183 | 0.686048
63095.73445 | 0.676282 | -30.823744 | 0.566537
79432.82347 | 0.663729 | -39.207232 | 0.798103
100000 | 0.667565 | -50.078577 | 0.745465
125892.5412 | 0.151417 | -62.509079 | 0.659393
158489.3192 | 0.374397 | -81.253907 | 0.496641
199526.2315 | 0.089797 | -102.678953 | 0.716535
251188.6432 | -0.772346 | -130.667857 | 0.676459
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
