MelansonTech/Melanson-Tech-Isolated-Shunt-Amplifier/Revision 1/TestData/BodePlots/SI8921B/1khz-800khz Gain 100x  0r010Shunt_4.7nf output filt opamp caps 20pf.xlsx

Untitled | Untitled 1 | Untitled 2 | Untitled 3
1000 | 0.004811 | -0.046745 | 0.363857
1258.925412 | 0.089252 | -0.276737 | 0.347227
1584.893192 | 0.039728 | -0.182683 | 0.365636
1995.262315 | 0.045434 | -0.375742 | 0.393248
2511.886432 | 0.07979 | -1.455223 | 0.305356
3162.27766 | 0.065163 | -0.710188 | 0.456518
3981.071706 | 0.071248 | -0.81137 | 0.386913
5011.872336 | 0.164851 | -1.515077 | 0.396942
6309.573445 | 0.164198 | -1.939148 | 0.410263
7943.282347 | 0.243045 | -2.510131 | 0.324613
10000 | 0.280872 | -3.814038 | 0.444799
12589.25412 | 0.332397 | -5.318539 | 0.424053
15848.93193 | 0.395076 | -7.314788 | 0.547736
19952.62315 | 0.436421 | -9.445972 | 0.447654
25118.86431 | 0.566468 | -13.389824 | 0.552351
31622.7766 | 0.520482 | -16.333149 | 0.517819
39810.71706 | 0.574132 | -20.885493 | 0.473455
50118.72336 | 0.632937 | -25.795056 | 0.684648
63095.73445 | 0.644596 | -34.790591 | 0.615435
79432.82347 | 0.622192 | -44.016385 | 0.583802
100000 | 0.560356 | -56.32191 | 0.577209
125892.5412 | 0.119486 | -69.463178 | 0.572266
158489.3192 | 0.18158 | -90.842314 | 0.787099
199526.2315 | -0.361088 | -114.843565 | 0.716259
251188.6432 | -1.515335 | -144.30767 | 1.150163
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
