MelansonTech/Melanson-Tech-Isolated-Shunt-Amplifier/Simulation/Amplifer.asc

C1: cap; 18pF
C2: cap; 2.2n
C3: cap; 3p
C4: cap; 3p
C5: cap; 1n
R1: res; 10K
R2: res; 8.1K
R3: res; 8.1K
R4: res; 10K
R5: res; 10k
R6: res; 10k
R7: res; 1410
R8: res; 10k
R9: res; 50
R10: res; 156.666
U1: opamp2; OPA197
U2: opamp2; OPA197
V1: voltage; 12
V2: voltage; 6
V3: voltage; AC 1
Named nets: 0, 12v, 6v
.lib "E:\\OneDrive\\Shawn\\Circuit Studio\\LtSpice SIM Models\\OPAMPS\\OPA197IDBVT\\OPA197.LIB"
;tran 0.1
.ac dec 1000 10 1meg
